TacTac315/PIR_Ball_Balancing/Matlab_Annexe/Ball_position_demo.png

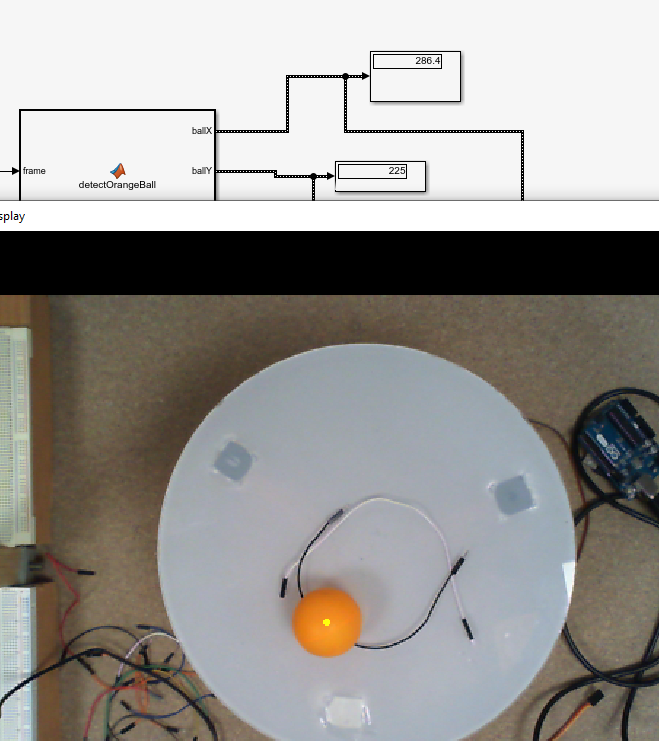
Matlab_Annexe/Ball_position_demo.png
