TacTac315/PIR_Ball_Balancing/Pieces_Modele/images/bras_vue-decouppe.png

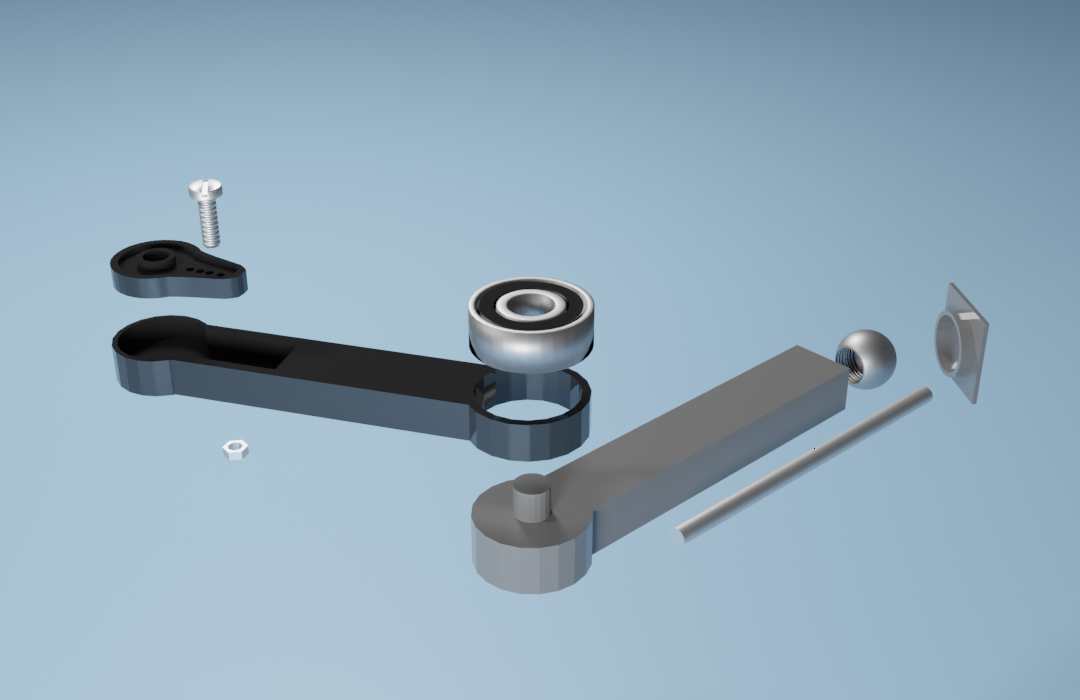
Pieces_Modele/images/bras_vue-decouppe.png
