TacTac315/PIR_Ball_Balancing/Pieces_Modele/images/system_complet.jpg

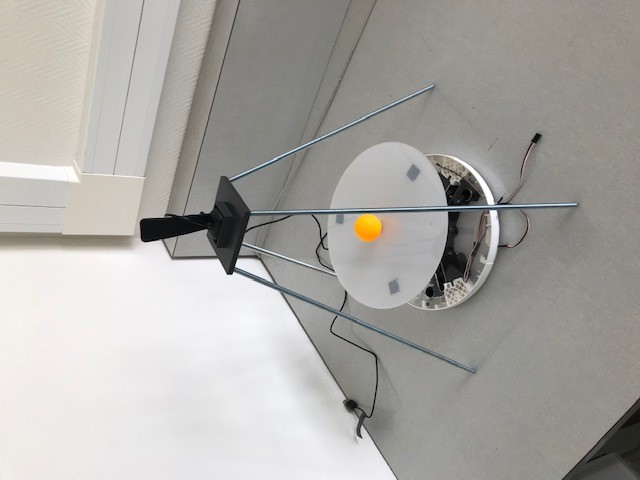
Pieces_Modele/images/system_complet.jpg
