TacTac315/PIR_Ball_Balancing/Pieces_Modele/images/systeme_complet.png

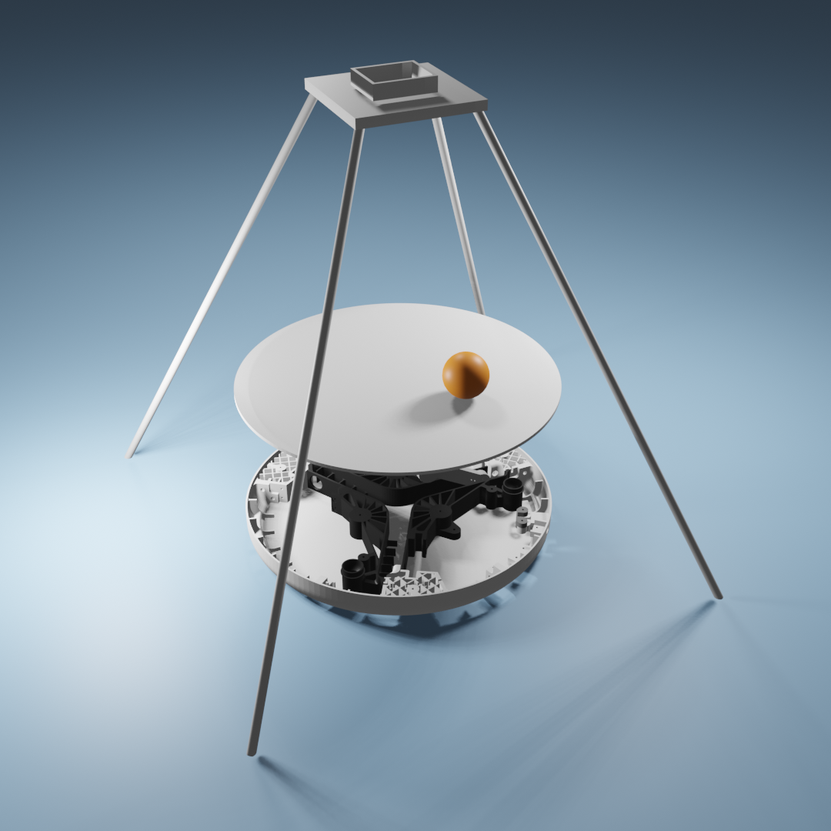
Pieces_Modele/images/systeme_complet.png
