TacTac315/PIR_Ball_Balancing/Report/src/imports/controller-circle.png

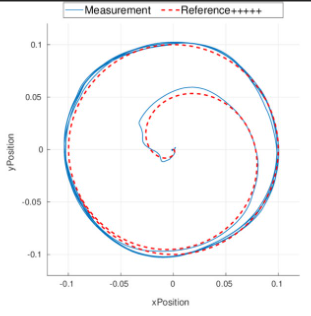
Report/src/imports/controller-circle.png
