TacTac315/PIR_Ball_Balancing/Pieces_Modele/contours/PIR_complet2.stl

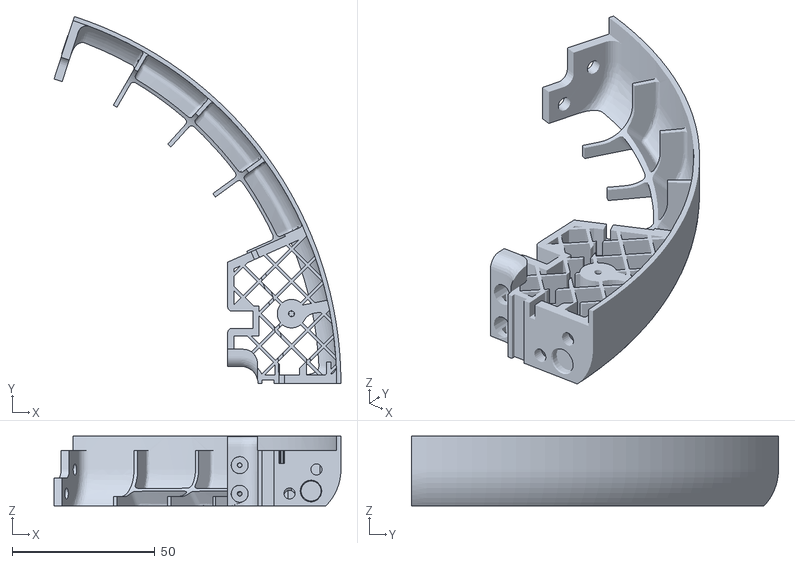
[picture p60: CAD file, 2023-03-21]
Pieces_Modele/contours/PIR_complet2.stl
100.4 x 128.4 x 24.5
