TacTac315/PIR_Ball_Balancing/Modele_3D_Simscape/MG995_ipt_28f8f921.STEP

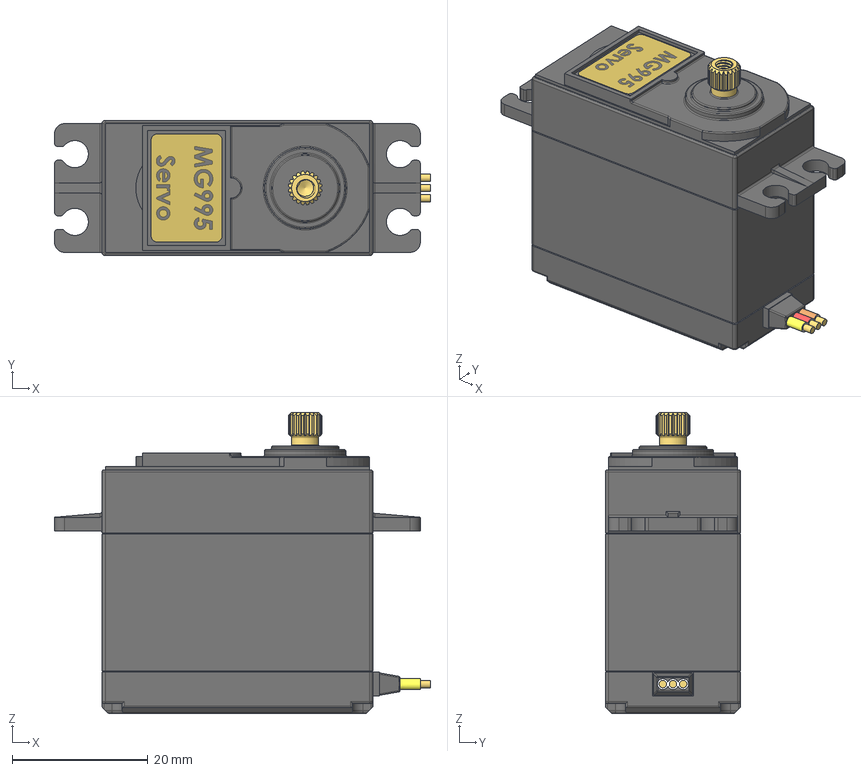
[picture p61: CAD file, 2023-05-16]
Modele_3D_Simscape/MG995_ipt_28f8f921.STEP
55.5 x 20.0 x 44.5 mm
